Callumpje1/WeatherAtHome/embedded/Api/HelloWorld.ino

#include <ESP8266WiFi.h>
#include <ESP8266HTTPClient.h>
#include <WiFiClient.h>

const char *ssid = "iotroam";
const char *password = "8iuZwH958F";

// Your Domain name with URL path or IP address with path
const char *serverName = "http://rnlrb-145-28-185-205.a.free.pinggy.online/php/api.php";

// the following variables are unsigned longs because the time, measured in
// milliseconds, will quickly become a bigger number than can be stored in an int.
unsigned long lastTime = 0;

unsigned long timerDelay = 5000;

void setup()
{
  Serial.begin(115200);

  WiFi.begin(ssid, password);
  Serial.println("Connecting");
  while (WiFi.status() != WL_CONNECTED)
  {
    delay(500);
    Serial.print(".");
  }
  Serial.println("");
  Serial.print("Connected to WiFi network with IP Address: ");
  Serial.println(WiFi.localIP());

  Serial.println("Timer set to 5 seconds (timerDelay variable), it will take 5 seconds before publishing the first reading.");
}

void loop()
{
  // Send an HTTP POST request every 10 minutes
  if ((millis() - lastTime) > timerDelay)
  {
    // Check WiFi connection status
    if (WiFi.status() == WL_CONNECTED)
    {
      WiFiClient client;
      HTTPClient http;

      // Your Domain name with URL path or IP address with path
      http.begin(client, serverName);

      // Specify content-type header
      http.addHeader("Content-Type", "application/x-www-form-urlencoded");
      // Data to send with HTTP POST
      String httpRequestData = "{ \
      \"temperature\": 20 \
      }";

      Serial.println(httpRequestData);

      // Send HTTP POST request
      int httpResponseCode = http.POST("?" + httpRequestData);

      Serial.print("HTTP Response code: ");
      Serial.println(http.getString());

      String payload = http.getString();
      Serial.println(payload);

      // Free resources
      http.end();
    }
    else
    {
      Serial.println("WiFi Disconnected");
    }
    lastTime = millis();
  }
}
